NoPantsNoLife/RM_Campus_Remote/Firmware_MCU/Core/Src/spi.c

/**
  ******************************************************************************
  * @file    spi.c
  * @brief   This file provides code for the configuration
  *          of the SPI instances.
  ******************************************************************************
  * @attention
  *
  * <h2><center>&copy; Copyright (c) 2021 STMicroelectronics.
  * All rights reserved.</center></h2>
  *
  * This software component is licensed by ST under BSD 3-Clause license,
  * the "License"; You may not use this file except in compliance with the
  * License. You may obtain a copy of the License at:
  *                        opensource.org/licenses/BSD-3-Clause
  *
  ******************************************************************************
  */

/* Includes ------------------------------------------------------------------*/
#include "spi.h"

/* SPI1 init function */
void MX_SPI1_Init(void)
{
  LL_SPI_InitTypeDef SPI_InitStruct = {0};

  LL_GPIO_InitTypeDef GPIO_InitStruct = {0};

  /* Peripheral clock enable */
  LL_APB2_GRP1_EnableClock(LL_APB2_GRP1_PERIPH_SPI1);

  LL_APB2_GRP1_EnableClock(LL_APB2_GRP1_PERIPH_GPIOA);
  /**SPI1 GPIO Configuration
  PA5   ------> SPI1_SCK
  PA6   ------> SPI1_MISO
  PA7   ------> SPI1_MOSI
  */
  GPIO_InitStruct.Pin = LL_GPIO_PIN_5|LL_GPIO_PIN_7;
  GPIO_InitStruct.Mode = LL_GPIO_MODE_ALTERNATE;
  GPIO_InitStruct.Speed = LL_GPIO_SPEED_FREQ_HIGH;
  GPIO_InitStruct.OutputType = LL_GPIO_OUTPUT_PUSHPULL;
  LL_GPIO_Init(GPIOA, &GPIO_InitStruct);

  GPIO_InitStruct.Pin = LL_GPIO_PIN_6;
  GPIO_InitStruct.Mode = LL_GPIO_MODE_FLOATING;
  LL_GPIO_Init(GPIOA, &GPIO_InitStruct);

  SPI_InitStruct.TransferDirection = LL_SPI_FULL_DUPLEX;
  SPI_InitStruct.Mode = LL_SPI_MODE_MASTER;
  SPI_InitStruct.DataWidth = LL_SPI_DATAWIDTH_8BIT;
  SPI_InitStruct.ClockPolarity = LL_SPI_POLARITY_LOW;
  SPI_InitStruct.ClockPhase = LL_SPI_PHASE_1EDGE;
  SPI_InitStruct.NSS = LL_SPI_NSS_SOFT;
  SPI_InitStruct.BaudRate = LL_SPI_BAUDRATEPRESCALER_DIV8;
  SPI_InitStruct.BitOrder = LL_SPI_MSB_FIRST;
  SPI_InitStruct.CRCCalculation = LL_SPI_CRCCALCULATION_DISABLE;
  SPI_InitStruct.CRCPoly = 10;
  LL_SPI_Init(SPI1, &SPI_InitStruct);

}

/* USER CODE BEGIN 1 */
uint8_t SPI_ReadWriteByte(SPI_TypeDef *SPIx, uint8_t TxData)
{
	/* Check if Tx buffer is empty */
	while (!LL_SPI_IsActiveFlag_TXE(SPIx));
	/* Write character in Data register. */
	LL_SPI_TransmitData8(SPIx, TxData);
 
	/* Check if Rx buffer is not empty */
	while (!LL_SPI_IsActiveFlag_RXNE(SPIx));
	/* received byte from SPI lines. */
	return LL_SPI_ReceiveData8(SPIx); 				    
}
/* USER CODE END 1 */

/************************ (C) COPYRIGHT STMicroelectronics *****END OF FILE****/
